MichaelBell/tt-audio-pmod/sim/PiezoOut.asc

B1: bv; V=3.3*((time/{period})-(int(time/{period}))<0.5+0.5*sin(2*pi*((time/{sweep})-(int(time/{sweep})))))
C1: cap; 100n
C2: cap; 12n
C3: cap; 147n
R1: res; 33
R2: res; 1k
R4: res; 37R
R6: res; 120
Named nets: out, 0
.tran 0 0.041 0.04 0.00000005
.param period=0.00001013/2
.step dec param sweep 0.001 0.0001 3
#.param sweep=0.001
